Lenka-12/EEE4022S/PCB/Audio_Digitizer/Manufucturing/Images/Total_Price.png

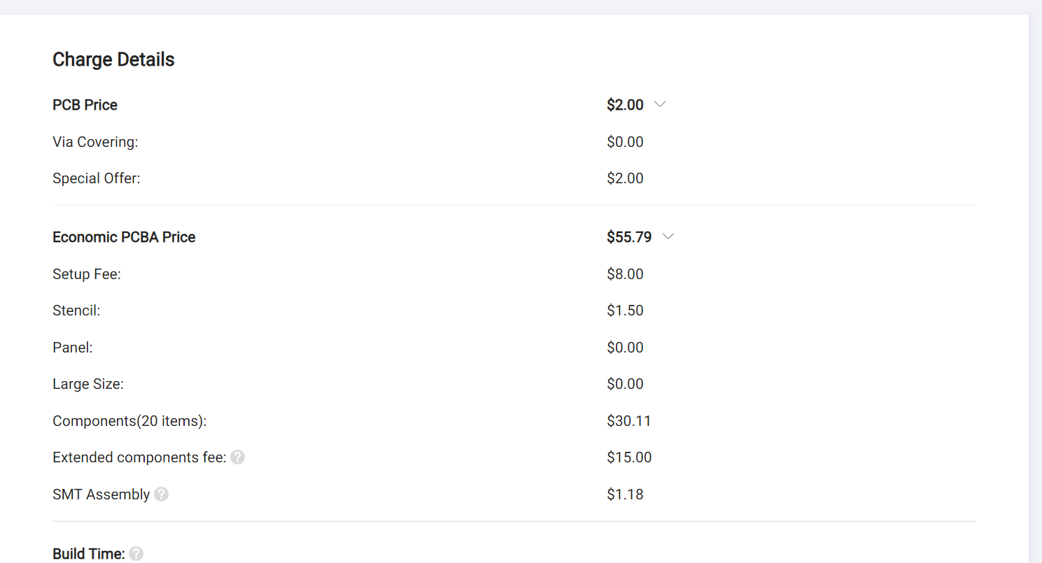
PCB/Audio_Digitizer/Manufucturing/Images/Total_Price.png
