Lenka-12/EEE4022S/EEE4022S_Final_Demo/Core/Src/main.c

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
/* Includes ------------------------------------------------------------------*/
#include "main.h"
#include "usb_device.h"

/* USER CODE BEGIN Includes */
#include "string.h"
#include "ADAU1978.h"
#include "usbd_cdc_if.h"
/* USER CODE END Includes */

/* USER CODE BEGIN PD */
#define SAMPLE_SIZE      2048
/* USER CODE END PD */

ADC_HandleTypeDef hadc3;
DMA_HandleTypeDef hdma_adc3;

I2C_HandleTypeDef hi2c1;

SAI_HandleTypeDef hsai_BlockA1;
SAI_HandleTypeDef hsai_BlockB1;
DMA_HandleTypeDef hdma_sai1_a;
DMA_HandleTypeDef hdma_sai1_b;

TIM_HandleTypeDef htim2;

/* USER CODE BEGIN PV */
ActiveADC_t adcx;
ADAU1978_t xHandle;
uint8_t start_tx;
uint8_t* pTxBuffer;
HAL_StatusTypeDef xStatus;

char* builtin = "ADC";
char* stereo   = "I2S";
char* tdm      = "TDM";
uint8_t adc_buffer[SAMPLE_SIZE*16];

/* USER CODE END PV */

void SystemClock_Config(void);
void PeriphCommonClock_Config(void);
static void MPU_Config(void);
static void MX_GPIO_Init(void);
static void MX_DMA_Init(void);
static void MX_I2C1_Init(void);
static void MX_SAI1_Init(void);
static void MX_ADC3_Init(void);
static void MX_TIM2_Init(void);
/* USER CODE BEGIN PFP */
void USB_RxCpltCallback(uint8_t* Buf, uint32_t *Len);
void USB_TxCpltCallback(uint8_t *Buf, uint32_t *Len);
void TDM4Init();
/* USER CODE END PFP */

/* USER CODE BEGIN 0 */
void TDM4Init(){
	// Enable all ADCs
	xHandle.block_power_sai = ADC_ENALL;
	// TDM4 Left Justified
	xHandle.sai_ctrl0 = SAI_CTRL0_TDM4|SAI_CTRL0_SDATA_FMT_LJ;
	// 24-bit data on 32 bit SLOT, LRCK pulse
	xHandle.sai_ctrl1  = SAI_CTRL1_DW_24_BITS | SAI_CTRL1_SW_32_BCKS| SAI_CTRL1_LR_MODE_PULSE;
	// enable HPF for all
	xHandle.dc_hpf_cal = DC_HPF_ALL;
	// Enable output for all
	xHandle.sai_overtemp = SAI_DRV_ALL;
	xHandle.gain_db = 40.125;
}
/* USER CODE END 0 */

/**
  * @brief  The application entry point.
  * @retval int
  */
int main(void)
{

  /* USER CODE BEGIN 1 */
	pTxBuffer = &adc_buffer[0];
	adcx = NONE;
	start_tx = 0;
	Audio_ADC_StructInit(&xHandle);
	TDM4Init();
  /* USER CODE END 1 */

  /* MPU Configuration--------------------------------------------------------*/
  MPU_Config();

  /* MCU Configuration--------------------------------------------------------*/

  /* Reset of all peripherals, Initializes the Flash interface and the Systick. */
  HAL_Init();

  /* Configure the system clock */
  SystemClock_Config();

  /* Configure the peripherals common clocks */
  PeriphCommonClock_Config();

  /* Initialize all configured peripherals */
  MX_GPIO_Init();
  MX_DMA_Init();
  MX_I2C1_Init();
  MX_SAI1_Init();
  MX_USB_DEVICE_Init();
  MX_ADC3_Init();
  MX_TIM2_Init();
  /* USER CODE BEGIN 2 */
    xStatus = Audio_ADC_Calibrate();
    if (xStatus != HAL_OK){
  	  //Error_Handler();
    }
    xStatus = Audio_ADC_Init(&xHandle);
    if (xStatus != HAL_OK){
  	  Error_Handler();
    }
  /* USER CODE END 2 */

  /* Infinite loop */
  /* USER CODE BEGIN WHILE */
  while (1)
  {
    /* USER CODE END WHILE */

    /* USER CODE BEGIN 3 */
	  HAL_Delay(100);
  }
  /* USER CODE END 3 */
}

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
/* USER CODE BEGIN 4 */
void HAL_GPIO_EXTI_Callback(uint16_t GPIO_Pin){
	if (GPIO_Pin == GPIO_PIN_13){
		start_tx = 1;
	}
}
void HAL_SAI_RxCpltCallback(SAI_HandleTypeDef *hsai){
	pTxBuffer = &adc_buffer[0];
	if (hsai ==  &hsai_BlockB1){
		// PCM1808 Active
		if ((start_tx == 1) && (adcx == PCM1808)){
			start_tx = 0;
			HAL_SAI_DMAStop(hsai);
			CDC_Transmit_FS(pTxBuffer, SAMPLE_SIZE*8);
		}
	}
	else if (hsai ==  &hsai_BlockA1){
		// ADA1978 ACTIVE
		if ((start_tx == 1) && (adcx == ADAU1978)){
			start_tx = 0;
			HAL_SAI_DMAStop(hsai);
			CDC_Transmit_FS(pTxBuffer, SAMPLE_SIZE*16);
		}
	}
}
void HAL_ADC_ConvCpltCallback(ADC_HandleTypeDef* hadc){
	pTxBuffer = &adc_buffer[0];
	if ((start_tx == 1) && (adcx == BUILTIN)){
		start_tx = 0;
		HAL_ADC_Stop_DMA(hadc);
		HAL_TIM_Base_Stop(&htim2);
		CDC_Transmit_FS(pTxBuffer, SAMPLE_SIZE*2);
	}
	else {
		HAL_ADC_Stop_DMA(hadc);
		HAL_TIM_Base_Stop(&htim2);
		HAL_ADC_Start_DMA(hadc,(uint32_t*)pTxBuffer, SAMPLE_SIZE*2);
		HAL_TIM_Base_Start(&htim2);
	}
}
void USB_RxCpltCallback(uint8_t* Buf, uint32_t *Len){
	pTxBuffer = &adc_buffer[0];
	if (strcmp(builtin, (char*)Buf) == 0){
		adcx = BUILTIN;
		HAL_GPIO_WritePin(LD1_GPIO_Port, LD1_Pin, GPIO_PIN_SET);
		HAL_ADC_Start_DMA(&hadc3, (uint32_t*)pTxBuffer, SAMPLE_SIZE*2);
		HAL_TIM_Base_Start(&htim2);
	}
	else if(strcmp(stereo, (char*)Buf) == 0){
		adcx = PCM1808;
		HAL_GPIO_WritePin(LD2_GPIO_Port, LD2_Pin, GPIO_PIN_SET);
		HAL_SAI_Receive_DMA(&hsai_BlockB1, pTxBuffer, SAMPLE_SIZE*2);
	}
	else if(strcmp(tdm, (char*)Buf) == 0){
		adcx = ADAU1978;
		HAL_GPIO_WritePin(LD3_GPIO_Port, LD3_Pin, GPIO_PIN_SET);
		HAL_SAI_Receive_DMA(&hsai_BlockA1, pTxBuffer, SAMPLE_SIZE*4);
	}
	else {
		adcx = NONE;
		HAL_GPIO_WritePin(LD1_GPIO_Port, LD1_Pin, GPIO_PIN_RESET);
		HAL_GPIO_WritePin(LD2_GPIO_Port, LD2_Pin, GPIO_PIN_RESET);
		HAL_GPIO_WritePin(LD3_GPIO_Port, LD3_Pin, GPIO_PIN_RESET);
	}
}
void USB_TxCpltCallback(uint8_t *Buf, uint32_t *Len){
	if (adcx == BUILTIN){
		HAL_GPIO_WritePin(LD1_GPIO_Port, LD1_Pin, GPIO_PIN_RESET);
		adcx = NONE;
	}
	else if (adcx == PCM1808){
		HAL_GPIO_WritePin(LD2_GPIO_Port, LD2_Pin, GPIO_PIN_RESET);
		adcx = NONE;
	}
	else if (adcx == ADAU1978){
		HAL_GPIO_WritePin(LD3_GPIO_Port, LD3_Pin, GPIO_PIN_RESET);
		adcx = NONE;
	}
}
/* USER CODE END 4 */

 /* MPU Configuration */

void MPU_Config(void)
{
  MPU_Region_InitTypeDef MPU_InitStruct = {0};

  /* Disables the MPU */
  HAL_MPU_Disable();

  /** Initializes and configures the Region and the memory to be protected
  */
  MPU_InitStruct.Enable = MPU_REGION_ENABLE;
  MPU_InitStruct.Number = MPU_REGION_NUMBER0;
  MPU_InitStruct.BaseAddress = 0x0;
  MPU_InitStruct.Size = MPU_REGION_SIZE_4GB;
  MPU_InitStruct.SubRegionDisable = 0x87;
  MPU_InitStruct.TypeExtField = MPU_TEX_LEVEL0;
  MPU_InitStruct.AccessPermission = MPU_REGION_NO_ACCESS;
  MPU_InitStruct.DisableExec = MPU_INSTRUCTION_ACCESS_DISABLE;
  MPU_InitStruct.IsShareable = MPU_ACCESS_SHAREABLE;
  MPU_InitStruct.IsCacheable = MPU_ACCESS_NOT_CACHEABLE;
  MPU_InitStruct.IsBufferable = MPU_ACCESS_NOT_BUFFERABLE;

  HAL_MPU_ConfigRegion(&MPU_InitStruct);
  /* Enables the MPU */
  HAL_MPU_Enable(MPU_PRIVILEGED_DEFAULT);

}

/**
  * @brief  This function is executed in case of error occurrence.
  * @retval None
  */
void Error_Handler(void)
{
  /* USER CODE BEGIN Error_Handler_Debug */
  /* User can add his own implementation to report the HAL error return state */
  __disable_irq();
  while (1)
  {
  }
  /* USER CODE END Error_Handler_Debug */
}

#ifdef  USE_FULL_ASSERT
/**
  * @brief  Reports the name of the source file and the source line number
  *         where the assert_param error has occurred.
  * @param  file: pointer to the source file name
  * @param  line: assert_param error line source number
  * @retval None
  */
void assert_failed(uint8_t *file, uint32_t line)
{
  /* USER CODE BEGIN 6 */
  /* User can add his own implementation to report the file name and line number,
     ex: printf("Wrong parameters value: file %s on line %d\r\n", file, line) */
  /* USER CODE END 6 */
}
#endif /* USE_FULL_ASSERT */
