Lenka-12/EEE4022S/EEE4022S_Final_Demo/Core/Inc/main.h

#define LD1_Pin GPIO_PIN_0
#define LD1_GPIO_Port GPIOB
#define LD3_Pin GPIO_PIN_14
#define LD3_GPIO_Port GPIOB
#define LD2_Pin GPIO_PIN_7
#define LD2_GPIO_Port GPIOB
